lambdakb/keyboard-lk7d/output/pcb/img/lk7d-pcb-bottom.png

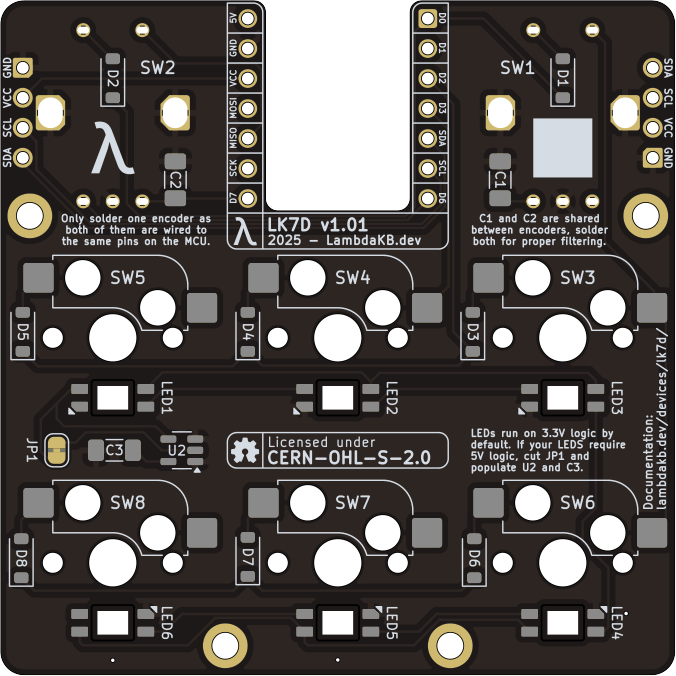
output/pcb/img/lk7d-pcb-bottom.png
