lambdakb/keyboard-lk7d/output/pcb/img/lk7d-pcb-top.png

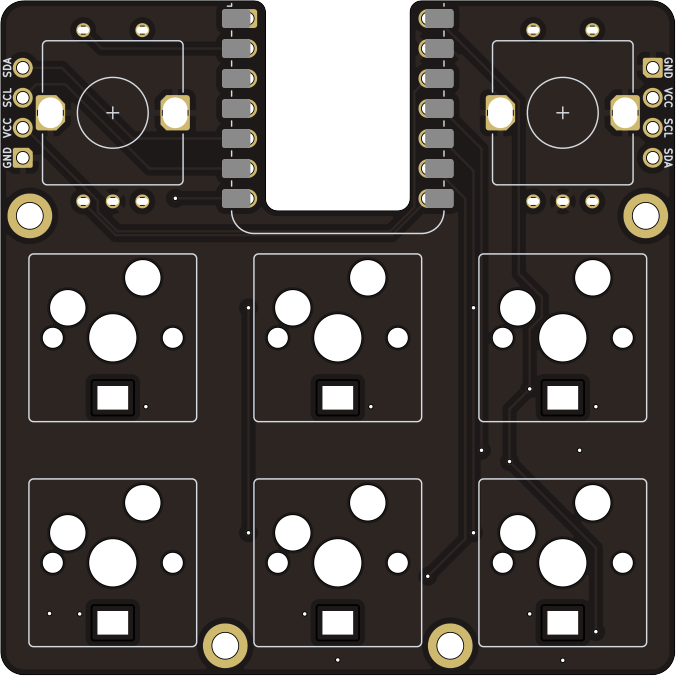
output/pcb/img/lk7d-pcb-top.png
