lambdakb/keyboard-lk7d/output/plate/img/lk7d-plate-bottom.png

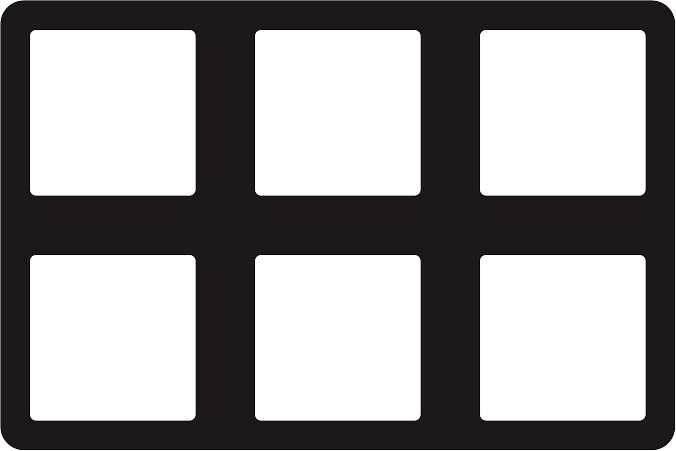
output/plate/img/lk7d-plate-bottom.png
